ai6ym/t41/software/SDT_Main/MenuProc.cpp

#ifndef BEENHERE
#include "SDT.h"
#endif

#if defined(USE_JSON)
#include "JSON.h"
#endif // USE_JSON

// Updates by KF5N to CalibrateOptions() function. July 20, 2023
// Updated receive calibration code to clean up graphics.  KF5N August 3, 2023

// ==============  AFP 10-22-22 ==================
/*****
  Purpose: Present the Calibrate options available and return the selection

  Parameter list:
    void

  Return value
   void
*****/
int CalibrateOptions(int IQChoice) {
  int val;
  int32_t increment = 100L;
  tft.fillRect(SECONDARY_MENU_X, MENUS_Y, EACH_MENU_WIDTH + 30, CHAR_HEIGHT, RA8875_BLACK);
  //  float transmitPowerLevelTemp;  //AFP 05-11-23
  switch (IQChoice) {

    case 0:  // Calibrate Frequency  - uses WWV
      freqCorrectionFactor = GetEncoderValueLive(-200000, 200000, freqCorrectionFactor, increment, (char *)"Freq Cal: ");
      if (freqCorrectionFactor != freqCorrectionFactorOld) {
        si5351.init(SI5351_LOAD_CAPACITANCE, Si_5351_crystal, freqCorrectionFactor); // KI3P July 27 2024, updated to mirror Setup()
        MyDelay(100L); // KI3P July 27 2024, updated to mirror Setup()
        si5351.drive_strength(SI5351_CLK0, SI5351_DRIVE_CURRENT);  // KI3P July 27 2024, updated to mirror Setup()
        si5351.drive_strength(SI5351_CLK1, SI5351_DRIVE_CURRENT);  // KI3P July 27 2024, updated to mirror Setup()
        si5351.drive_strength(SI5351_CLK2, SI5351_DRIVE_CURRENT);  // KF5N July 10 2023
        si5351.set_ms_source(SI5351_CLK0, SI5351_PLLA); // KI3P July 27 2024, updated to mirror Setup()
        si5351.set_ms_source(SI5351_CLK1, SI5351_PLLA); // KI3P July 27 2024, updated to mirror Setup()
        
        SetFreq();
        MyDelay(10L);
        freqCorrectionFactorOld = freqCorrectionFactor;
      }
      val = ReadSelectedPushButton();
      if (val != BOGUS_PIN_READ) {        // Any button press??
        val = ProcessButtonPress(val);    // Use ladder value to get menu choice
        if (val == MENU_OPTION_SELECT) {  // Yep. Make a choice??
          tft.fillRect(SECONDARY_MENU_X, MENUS_Y, EACH_MENU_WIDTH + 35, CHAR_HEIGHT, RA8875_BLACK);
          EEPROMWrite();
          calibrateFlag = 0;
          IQChoice = 5;
          return IQChoice;
        }
      }
      break;

    case 1:  // CW PA Cal
      if (keyPressedOn == 1 && xmtMode == CW_MODE) {
        //================  CW Transmit Mode Straight Key ===========
        if (digitalRead(KEYER_DIT_INPUT_TIP) == LOW && xmtMode == CW_MODE && keyType == 0) {  //Straight Key
          #ifdef V12HWR
          // Calibration power is 
          EEPROMData.powerLevel = CAL_POWER_LEVEL_W; // adjustment is 0 for this power level, so don't calculate it
          currentRF_OutAtten = XAttenCW[currentBand];
          SetRF_OutAtten(currentRF_OutAtten);
          Clk2SetFreq = centerFreq*SI5351_FREQ_MULT + (long long)(CWToneOffsetsHz[EEPROMData.CWToneIndex]*SI5351_FREQ_MULT);
          si5351.set_freq(Clk2SetFreq, SI5351_CLK2);
          si5351.output_enable(SI5351_CLK2, 1);
          digitalWrite(CW_ON_OFF, CW_ON);  // LOW = CW off, HIGH = CW on
          digitalWrite(XMIT_MODE, XMIT_CW); // KI3P, July 28, 2024
          #else
          powerOutCW[currentBand] = (-.0133 * transmitPowerLevel * transmitPowerLevel + .7884 * transmitPowerLevel + 4.5146) * CWPowerCalibrationFactor[currentBand];
          CW_ExciterIQData();
          SetFreq();                 //  AFP 10-02-22
          digitalWrite(MUTE, HIGH);  // KI3P, no MUTE function in V12
          #endif
          xrState = TRANSMIT_STATE;
          ShowTransmitReceiveStatus();
          modeSelectInR.gain(0, 0);
          modeSelectInL.gain(0, 0);
          modeSelectInExR.gain(0, 0);
          modeSelectOutL.gain(0, 0);
          modeSelectOutR.gain(0, 0);
          modeSelectOutExL.gain(0, 0);
          modeSelectOutExR.gain(0, 0);
        }
      }
      #ifdef V12HWR
      XAttenCW[currentBand] = GetEncoderValueLiveInt(0,63,XAttenCW[currentBand],1,(char *)"CW PA Att.");
      currentRF_OutAtten = XAttenCW[currentBand];
      if (currentRF_OutAtten > 63) currentRF_OutAtten = 63;
      if (currentRF_OutAtten < 0) currentRF_OutAtten = 0;
      SetRF_OutAtten(currentRF_OutAtten);
      #else
      CWPowerCalibrationFactor[currentBand] = GetEncoderValueLive(-2.0, 2.0, CWPowerCalibrationFactor[currentBand], 0.001, (char *)"CW PA Cal: ");
      powerOutCW[currentBand] = (-.0133 * transmitPowerLevel * transmitPowerLevel + .7884 * transmitPowerLevel + 4.5146) * CWPowerCalibrationFactor[currentBand];  // AFP 10-21-22
      #endif
      val = ReadSelectedPushButton();
      if (val != BOGUS_PIN_READ) {        // Any button press??
        val = ProcessButtonPress(val);    // Use ladder value to get menu choice
        if (val == MENU_OPTION_SELECT) {  // Yep. Make a choice??
          digitalWrite(CW_ON_OFF, CW_OFF);
          tft.fillRect(SECONDARY_MENU_X, MENUS_Y, EACH_MENU_WIDTH + 35, CHAR_HEIGHT, RA8875_BLACK);
          #ifndef V12HWR
          EEPROMData.CWPowerCalibrationFactor[currentBand] = CWPowerCalibrationFactor[currentBand];
          #else
          EEPROMData.XAttenCW[currentBand] = XAttenCW[currentBand];
          #endif 
          EEPROMWrite();
          calibrateFlag = 0;
          IQChoice = 5;
          return IQChoice;
        }
      }
      break;
    case 2:                  // IQ Receive Cal - Gain and Phase
      DoReceiveCalibrate();  // This function was significantly revised.  KF5N August 16, 2023
      IQChoice = 5;
      break;
    case 3:               // IQ Transmit Cal - Gain and Phase  //AFP 2-21-23
      DoXmitCalibrate();  // This function was significantly revised.  KF5N August 16, 2023
      IQChoice = 5;
      break;
    case 4:  // SSB PA Cal
      #ifdef V12HWR
      EEPROMData.powerLevel = CAL_POWER_LEVEL_W; // adjustment is 0 for this power level, so don't calculate it
      XAttenSSB[currentBand] = GetEncoderValueLiveInt(0,63,XAttenSSB[currentBand],1,(char *)"SSB PA Att.");
      currentRF_OutAtten = XAttenSSB[currentBand];
      if (currentRF_OutAtten > 63) currentRF_OutAtten = 63;
      if (currentRF_OutAtten < 0) currentRF_OutAtten = 0;
      SetRF_OutAtten(currentRF_OutAtten);
      #else
      SSBPowerCalibrationFactor[currentBand] = GetEncoderValueLive(-2.0, 2.0, SSBPowerCalibrationFactor[currentBand], 0.001, (char *)"SSB PA Cal: ");
      powerOutSSB[currentBand] = (-.0133 * transmitPowerLevel * transmitPowerLevel + .7884 * transmitPowerLevel + 4.5146) * SSBPowerCalibrationFactor[currentBand];  // AFP 10-21-22
      #endif
      val = ReadSelectedPushButton();
      if (val != BOGUS_PIN_READ) {        // Any button press??
        val = ProcessButtonPress(val);    // Use ladder value to get menu choice
        if (val == MENU_OPTION_SELECT) {  // Yep. Make a choice??
          tft.fillRect(SECONDARY_MENU_X, MENUS_Y, EACH_MENU_WIDTH + 35, CHAR_HEIGHT, RA8875_BLACK);
          #ifdef V12HWR
          EEPROMData.XAttenSSB[currentBand] = XAttenSSB[currentBand];
          #endif
          EEPROMWrite();
          calibrateFlag = 0;
          IQChoice = 5;
          return IQChoice;
        }
      }
      break;  // Missing break.  KF5N August 12, 2023

    case 5:
      //EraseMenus();
      RedrawDisplayScreen();
      currentFreq = TxRxFreq = centerFreq + NCOFreq;
      DrawBandWidthIndicatorBar();  // AFP 10-20-22
      ShowFrequency();
      BandInformation();
      calibrateFlag = 0;
      // centerTuneFlag = 1;  Not used in revised tuning scheme.  July 22, 2023
      modeSelectOutExL.gain(0, 0);
      modeSelectOutExR.gain(0, 0);
      ShowSpectrum();  //KF5N
      break;

    default:  // Cancelled choice
      micChoice = -1;
      break;
  }
  return 1;
}
// ==============  AFP 10-22-22 ==================
/*****
  Purpose: Present the CW options available and return the selection

  Parameter list:
    void

  Return value
    int           an index into the band array
*****/
int CWOptions()  // new option for Sidetone and Delay JJP 9/1/22
{

  switch (secondaryMenuIndex) {
    case 0:  // WPM
      SetWPM();
      SetTransmitDitLength(currentWPM);  //Afp 09-22-22     // JJP 8/19/23
      break;

    case 1:  // Straight key:
      EEPROMData.keyType = keyType = 0;
      //      SetKeyType();  // Straight key or keyer? Stored in EEPROMData.keyType; no heap/stack variable
      //      SetKeyPowerUp();
      UpdateKeyTypeField();
      break;

    case 2:  // Keyer
      EEPROMData.keyType = keyType = 1;
      //      SetKeyType();  // Straight key or keyer? Stored in EEPROMData.keyType; no heap/stack variable
      //      SetKeyPowerUp();
      UpdateKeyTypeField();
      break;

    case 3:              // CW Filter BW:      // AFP 10-18-22
      SelectCWFilter();  // in CWProcessing    // AFP 10-18-22
      EraseMenus();
      RedrawDisplayScreen();
      ShowFrequency();
      DrawFrequencyBarValue();
      break;  // AFP 10-18-22

    case 4:            // Flip paddles
      DoPaddleFlip();  // Stored in EEPROM; variables paddleDit and paddleDah
      break;

    case 5:
      SelectCWToneOffset();
      break;

    case 6:  // Sidetone volume
             //  SetSidetoneVolume();
      SetSideToneVolume();
      break;

    case 7:                // new function JJP 9/1/22
      SetTransmitDelay();  // Transmit relay hold delay
      break;

    default:  // Cancel
      break;
  }
  return secondaryMenuIndex;
}

/*****
  Purpose: Set the loudness of the sidetone.

  Parameter list:
    void

  Return value
    void
*****/
void SetSidetoneVolume() {
  const char *loudness[] = { "Whisper", "Low", "Medium", "Loud", "Cancel" };
  int retVal;
  const float32_t sidetoneParameter[] = { 0.1, 0.25, 0.5, 1.0, 0.0 };  // Louder sidetone. G0ORX.  Old values -> { 0.0005, 0.001, 0.002, 0.004, 0.0 };  //  AFP 10-01-22

  retVal = SubmenuSelect(loudness, 4, sidetoneVolume);
  if (retVal == 4)  // Did they make a choice?
    return;         // Nope.

  sidetoneVolume = sidetoneParameter[retVal];

  EEPROMData.sidetoneVolume = sidetoneVolume;
  EEPROMWrite();
  RedrawDisplayScreen();
  ShowSpectrumdBScale();
}
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
